Priyanshjain24/EDL-2024/Software/STM32/Core/Src/FS-iA6B.c

/*
 * FS-iA6B.c
 *
 *  Created on: Feb 19, 2024
 *      Author: ksath
 */


#include "FS-iA6B.h"

unsigned char iBus_Check_CHKSUM(unsigned char* data, unsigned char len)
{
	unsigned short chksum = 0xffff;

	for(int i=0;i<len-2;i++)
	{
		chksum = chksum - data[i];
	}

	return ((chksum&0x00ff)==data[30]) && ((chksum>>8)==data[31]);
}

void iBus_Parsing(unsigned char* data, FSiA6B_iBus* iBus)
{
	iBus->RH = (data[2] | data[3]<<8) & 0x0fff;
	iBus->RV = (data[4] | data[5]<<8) & 0x0fff;
	iBus->LV = (data[6] | data[7]<<8) & 0x0fff;
	iBus->LH = (data[8] | data[9]<<8) & 0x0fff;
	iBus->SwA = (data[10] | data[11]<<8) & 0x0fff;
	iBus->SwC = (data[12] | data[13]<<8) & 0x0fff;
}
